DamarisMenfer/Noize_Raynaud_GasSensor/Spice/Trigger_Schmitt.asc

R1: res; 4.7k
R2: res; 100k
U1: LM741_NS
V1: voltage; 5
V2: voltage; 2.5
V3: voltage; SINE(2.5 1 10)
Named nets: 0, Vcc, Vseuil, Vin, Vout
.tran 1
Vb = Vseuil(1 + R1/R2) - Vout(R1/R2)
